ut-ras/Region-5-2017-2018/Region-5-2017-2018.ino

#include <Time.h>
#include <Arduino.h>
<<<<<<< HEAD
/*#include "testarrayLine.cpp"
#include "testGraph.cpp"
=======
//#include "testarrayLine.cpp"
//#include "testGraph.cpp"
#include "src/tests/testPointline.cpp"*/
#include "rgbsensor.h"
#include "testRGB.cpp"
#include "sensorbar.h"
//#include "src/tests/testPointline.cpp"
>>>>>>> 01994964d0b2952e89b2ca3a758c6b91656febcf

void setup() {  
    // put your setup code here, to run once:]
    Serial.begin(9600);
    //setupGraphTest();
<<<<<<< HEAD
    //setupTestArrayLine();
    setupRGBTest();
    }
/*void loop() {
  // put your main code here, to run repeatedly:
  loopArrayLineTest();
=======
    setupPointLineTest(0);
  //  setupTestArrayLine();
    }*/
void loop() {
  // put your main code here, to run repeatedly:
  //loopArrayLineTest();
  //loopPointLineTest();
  loopRGBTest();
>>>>>>> 01994964d0b2952e89b2ca3a758c6b91656febcf
  //loopGraphTest();

}

/*
void round1(){
	int[] inventory = new int[6];
  time_t t = now();
	if(whichSide() == Node::Color::yellow){
  //Collection
		turn(PI / 4);
   //collect across diagonal going from yellow to red
		for(int i = 0; i < 4; i++){
			forwardToIntersection();
			pickUpToken();
			updateInventory(storeToken(), inventory);
		}
		moveForward(distance across grey square);
		for(int i = 0; i < 4; i++){
			forwardToIntersection();
			pickUpToken();
			updateInventory(storeToken(), inventory);
		}
		depositIfEnough(Node::Color::red, 3, inventory[0]);
   //go to green
    turn(3 * PI / 4);
    forwardToIntersection();
    depositIfEnough(Node::Color::green, 3, inventory[1]);
    //go across to magenta
    turn(PI / 2);
    for(int i = 0; i < 4; i++){
      forwardToIntersection();
      pickUpToken();
      updateInventory(storeToken(), inventory);
    }
    moveForward(distance across grey square);
    for(int i = 0; i < 4; i++){
      forwardToIntersection();
      pickUpToken();
      updateInventory(storeToken(), inventory);
    }
    depositIfEnough(Node::Color::magenta, 3, inventory[4]);
    turn(PI/2);
    forwardToIntersection();
    depositIfEnough(Node::Color::cyan, 3, inventory[5]);
    //go across the diagonal from cyan to blue
    turn(3 * PI / 4);
    for(int i = 0; i < 4; i++){
      forwardToIntersection();
      pickUpToken();
      updateInventory(storeToken(), inventory);
    }
    moveForward(distance across grey square);
    for(int i = 0; i < 4; i++){
      forwardToIntersection();
      pickUpToken();
      updateInventory(storeToken(), inventory);
    }
    depositIfEnough(Node::Color::blue, 3, inventory[2]);
    //---------------------------------------------------



	} else{ // first color is red


	}
}

void round2(){
	int[] inventory = new int[6];
}

void round3(){
	int[] inventory = new int[7];
}

void forwardToIntersection(){
	while(getData() != getNextIntersection())
		moveForward();
}

void updateInventory(Node::Color c, int[] inventory){
  inventory[c]++;
}

void depositIfEnough(Node::Color c, int min, int current){
	if(current >= min)
		tokenControl::depositTokens();
}

Node::Color whichSide(){
	moveForward(distance to colored square);
	return getColor();
<<<<<<< HEAD
}
*/
