ut-ras/Region-5-2017-2018/R5MegaMain/src/drivers/motorController.cpp

#include "motorController.h"

motorController::motorController(int _boardAddress){

	speed = 0;

	Wire.onReceive(receiveEvent);
	Wire.begin(_boardAddress);
	//Attach the board to the shield
	Adafruit_MotorShield AFMS = Adafruit_MotorShield(0x61);

	//Attach the motors
	Adafruit_DCMotor *rightMotor = AFMS.getMotor(1);
	Adafruit_DCMotor *leftMotor = AFMS.getMotor(2);

	//Default frequency: 1.6 KHz
	AFMS.begin();
	//AFMS.begin(1000); //1000Hz for example

	//Initialize motors:
	rightMotor->setSpeed(0);
	leftMotor->setSpeed(0);
	rightMotor->run(FORWARD);
	leftMotor->run(FORWARD);
	rightMotor->run(RELEASE);
	leftMotor->run(RELEASE);
}

void motorController::setSpeed(uint8_t _speed){
	speed = _speed;
}

void motorController::stop(){
	rightMotor->run(RELEASE);
	leftMotor->run(RELEASE);
}

void motorController::moveForwardIndefinitely(){
	rightMotor->run(FORWARD);
	leftMotor->run(FORWARD);
	rightMotor->setSpeed(speed);
	rightMotor->setSpeed(speed);
}

void motorController::moveBackwardIndefinitely(){
	rightMotor->run(BACKWARD);
	leftMotor->run(BACKWARD);
	rightMotor->setSpeed(speed);
	rightMotor->setSpeed(speed);
}

void motorController::moveForward(double distance){
	rightMotor->run(FORWARD);
	leftMotor->run(FORWARD);
	rightMotor->setSpeed(speed);
	rightMotor->setSpeed(speed);
	//Have to get the encoders working
}

void motorController::moveBackward(double distance){
	rightMotor->run(BACKWARD);
	leftMotor->run(BACKWARD);
	rightMotor->setSpeed(speed);
	rightMotor->setSpeed(speed);
	//Have to make a encoder data receiver I think
}

void motorController::turn(double angleDegrees){
	if(angleDegrees > 0){
		rightMotor->run(BACKWARD);
		leftMotor->run(FORWARD);
		rightMotor->setSpeed(speed);
		leftMotor->setSpeed(speed);
		//Make something for the gyro to tell how much of an arc we have to cover
	} else if(angleDegrees < 0){
		rightMotor->run(FORWARD);
		leftMotor->run(BACKWARD);
		rightMotor->setSpeed(speed);
		leftMotor->setSpeed(speed);
	} else if(angleDegrees == 0){
		moveForward(distance);
	}
}

//Not part of the motorController class
//What happens when the Mega asks for it to move?
void receiveEvent(int numBytes){

}
