ut-ras/Region-5-2017-2018/R5MegaMain/src/drivers/motorController.h

#ifndef motorController_h
#define motorController_h

#include "Arduino.h"
#include <Wire.h>
#include <Adafruit_MotorShield.h>
#include "utility/Adafruit_MS_PWMServoDriver.h"

class motorController {
public:
	//Initializes the motor shield and i2c communication between
	//the Mega and the UNO controlling the shield
	motorController(int _boardAddress);

    //Moves forward a certain distance
    void moveForward(float distance);

    //Move backward a certain distance
    void moveBackward(float distance);

	//Stop the motors
	void stop();

    //Turn at an angle
    void turn(float angleDegrees);

	//I2C receive event
	void receiveEvent(int numbytes);

	void setSpeed(uint8_t _speed);

	void moveForwardIndefinitely();
	void moveBackwardsIndefinitely();

private:
	Adafruit_MotorShield AFMS;

	Adafruit_DCMotor *rightMotor;
	Adafruit_DCMotor *leftMotor;

	float oneRotation;

	uint8_t speed;

};

#endif
