ut-ras/Region-5-2017-2018/R5MegaMain/src/drivers/servo.cpp

#include "servo.h"
#include <Servo.h>

//servo inputs go from 10 - 180 , running below 10 results in constant slow rotation
servo::servo(int _servoPin){
	servoPos = 180;
	thisServo.attach(_servoPin);
	thisServo.write(servoPos);	//initialize the servo to the start servo position
	delay(100);
}

void servo::movePulley(double degrees){
	servoPos = degrees;
	thisServo.write(servoPos);
	delay(100);
}
