ut-ras/Region-5-2017-2018/R5MegaMain/tests/testRGB/testRGB.ino/testRGB.ino.ino

#include <Arduino.h>
#include "rgbsensor.h"
#include "Node.h"
rgbsensor* rgb;
void setup() {
  // put your setup code here, to run once:
  Serial.begin(9600);
  Serial.println("Color View Test!");

  rgb = new rgbsensor();
}

void loop() {
  // put your main code here, to run repeatedly:
  // put your main code here, to run repeatedly:
  Serial.println(rgb->colorTable[rgb->getColor()]);
  delay(2500);
}
