ut-ras/Region-5-2017-2018/R5MegaDrive/tests/basicMoveTest/MotorControl.h

#ifndef MOTORCONTROL_H
#define MOTORCONTROL_H
#include <Adafruit_MotorShield.h>
#include <PID_v1.h>
#include "utility/Adafruit_MS_PWMServoDriver.h"

#include "encoder.h"

//required libraries:
//Adafruit_MotorShield v2
//PID by Brett

enum Commands{FWD1, FWD2, FWD3, BACK1, BACK2, BACK3, LEFT, RIGHT, STOP};

class MotorControl {

public:
  MotorControl(int lA, int lB, int rA, int rB);
  void update();
  void setMotorMode(int c);

  encoder* getLeftEncoder();
  encoder* getRightEncoder();

private:

  void setMotorAction(char a);
  void setMotorSpeed(char s);
  void setMotorDirection(char d);
 
  void setPIDSpeed(int leftSpeed, int rightSpeed);
  void calculateVelocity();
  int normalizeSpeedForAFMS(double s);
  
  //Motor Variables
  double motorMaxSpeed = 950.0;
  char motorAction;
  int motorSpeed;
  int motorDirection;

  encoder* leftEncoder;
  encoder* rightEncoder;

  Adafruit_MotorShield *AFMS;
  Adafruit_DCMotor *myMotor;
  Adafruit_DCMotor *myOtherMotor;

  //PID Variables
  unsigned long prevTime;   //stored as milliseconds, converted to second in calculateVelocity

  int leftPrevEncoderPos;
  double leftSetpoint, leftVelocity, leftPower;
  double leftKp;
  double leftKi;
  double leftKd;
  PID * leftMotorPID;

  int rightPrevEncoderPos;
  double rightSetpoint, rightVelocity, rightPower;
  double rightKp;
  double rightKi;
  double rightKd;
  PID * rightMotorPID;

  // velocity averaging stuff
  const double numVSamples = 5;
  int vSampleCount = 0;
  double leftVSampleSum = 0;
  double rightVSampleSum = 0;
};

#endif
