ut-ras/Region-5-2017-2018/R5MegaDrive/tests/test2drive/encoder.h

#ifndef ENCODER_H
#define ENCODER_H

class encoder {

public:
  encoder(int pa, int pb);  //pinA MUST be interrupt capable
  int getPos();
  int updatePos();

private:
  int pinA, pinB;
  int pos;

};

#endif
