ut-ras/Region-5-2017-2018/R5MegaMain/tests/Region-5-2017-2018-temp/Region-5-2017-2018-temp.ino

#include <Time.h>
#include <Arduino.h>
#include "Graph.h"

void setup() {
  Serial.begin(9600);
  //Serial.println("Graph Test - setup");
  delay(1000);
}

void loop() {
  //Serial.println("Graph Test - main loop");
  delay(1000);
  
  Graph g;
  g.graphTest();
  
  delay(60000);
}
  
